dan-code1232/my-keeb/pcb/MY KEEB PCB FIXED.kicad_sch

## KiCad design pcb/MY KEEB PCB FIXED.kicad_sch (2026-08-29)

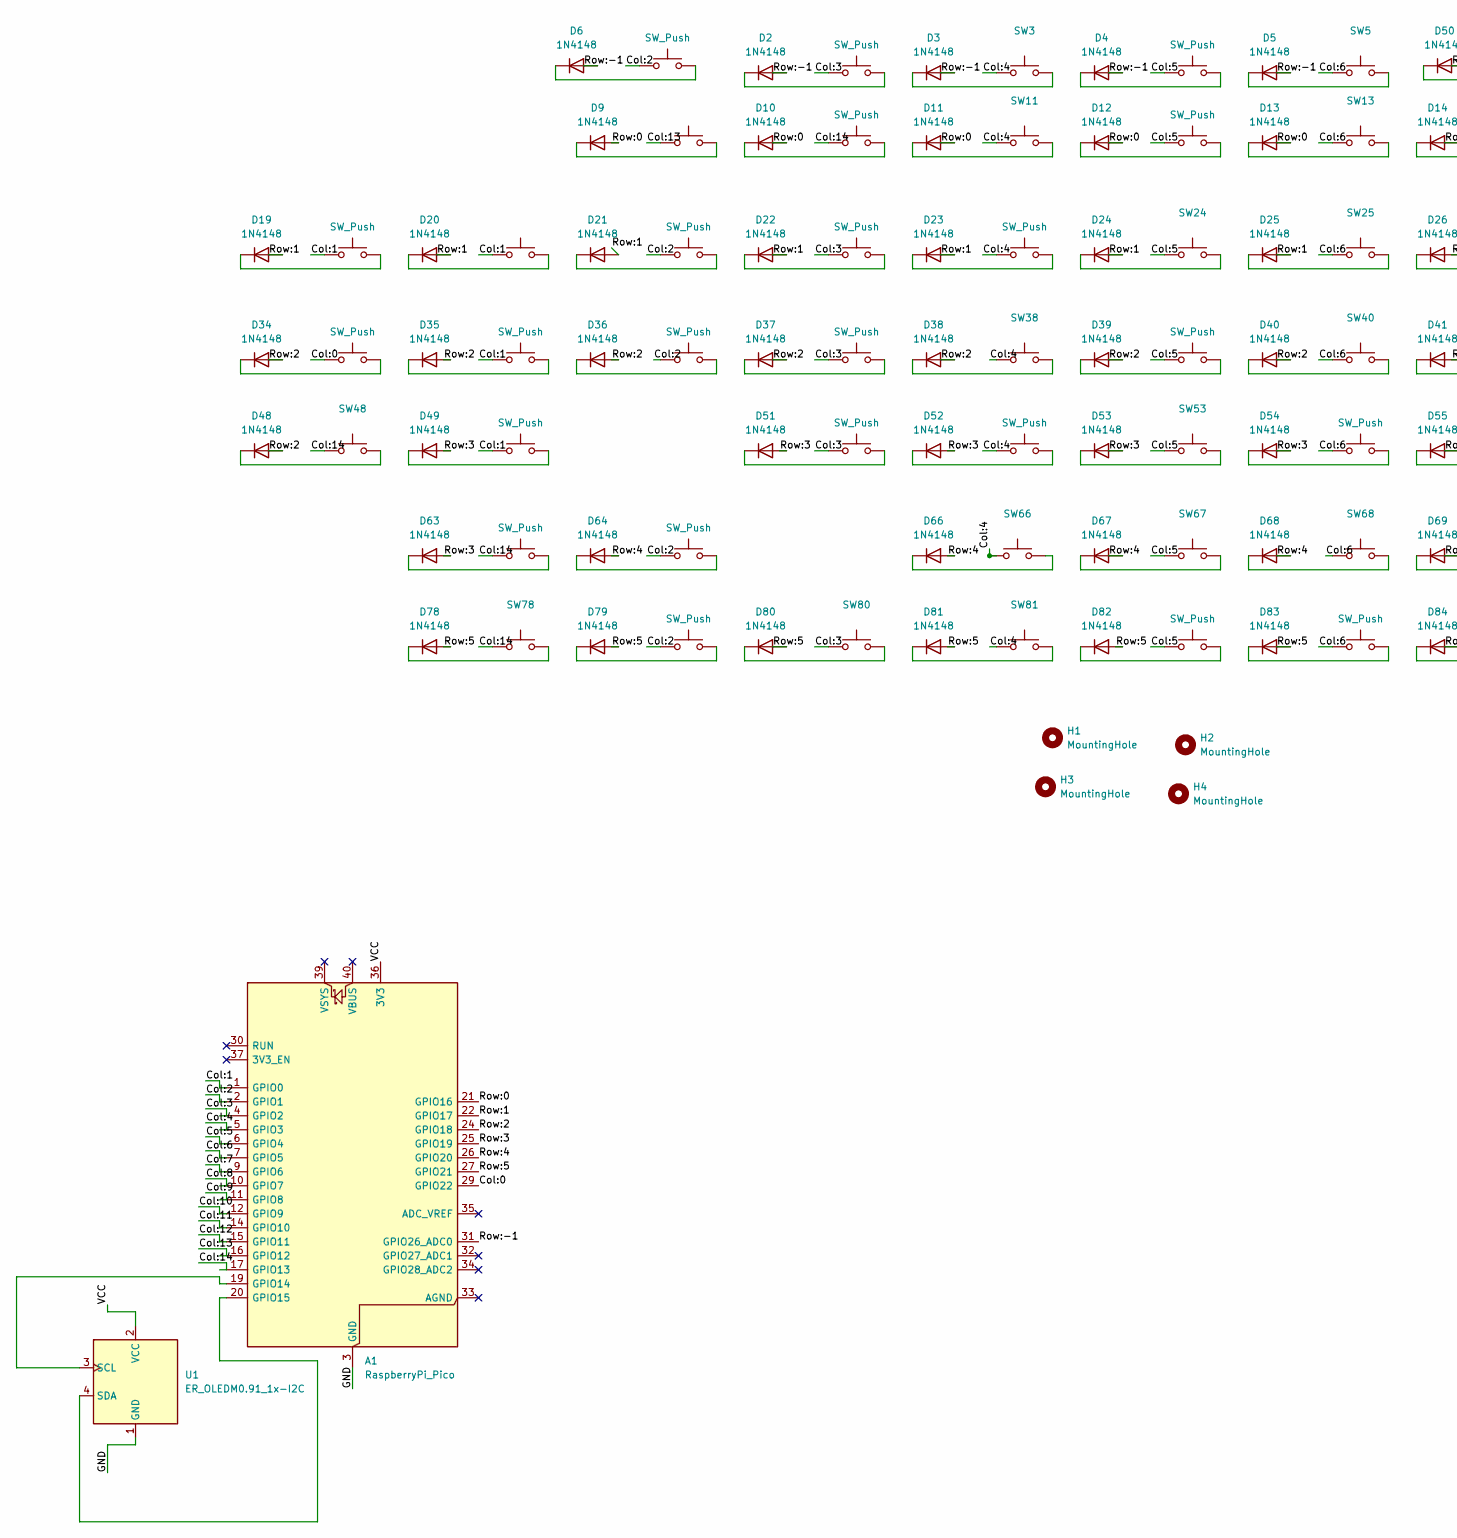
[picture p4: schematic MY KEEB PCB FIXED.kicad_sch, part in row 1, column 1]

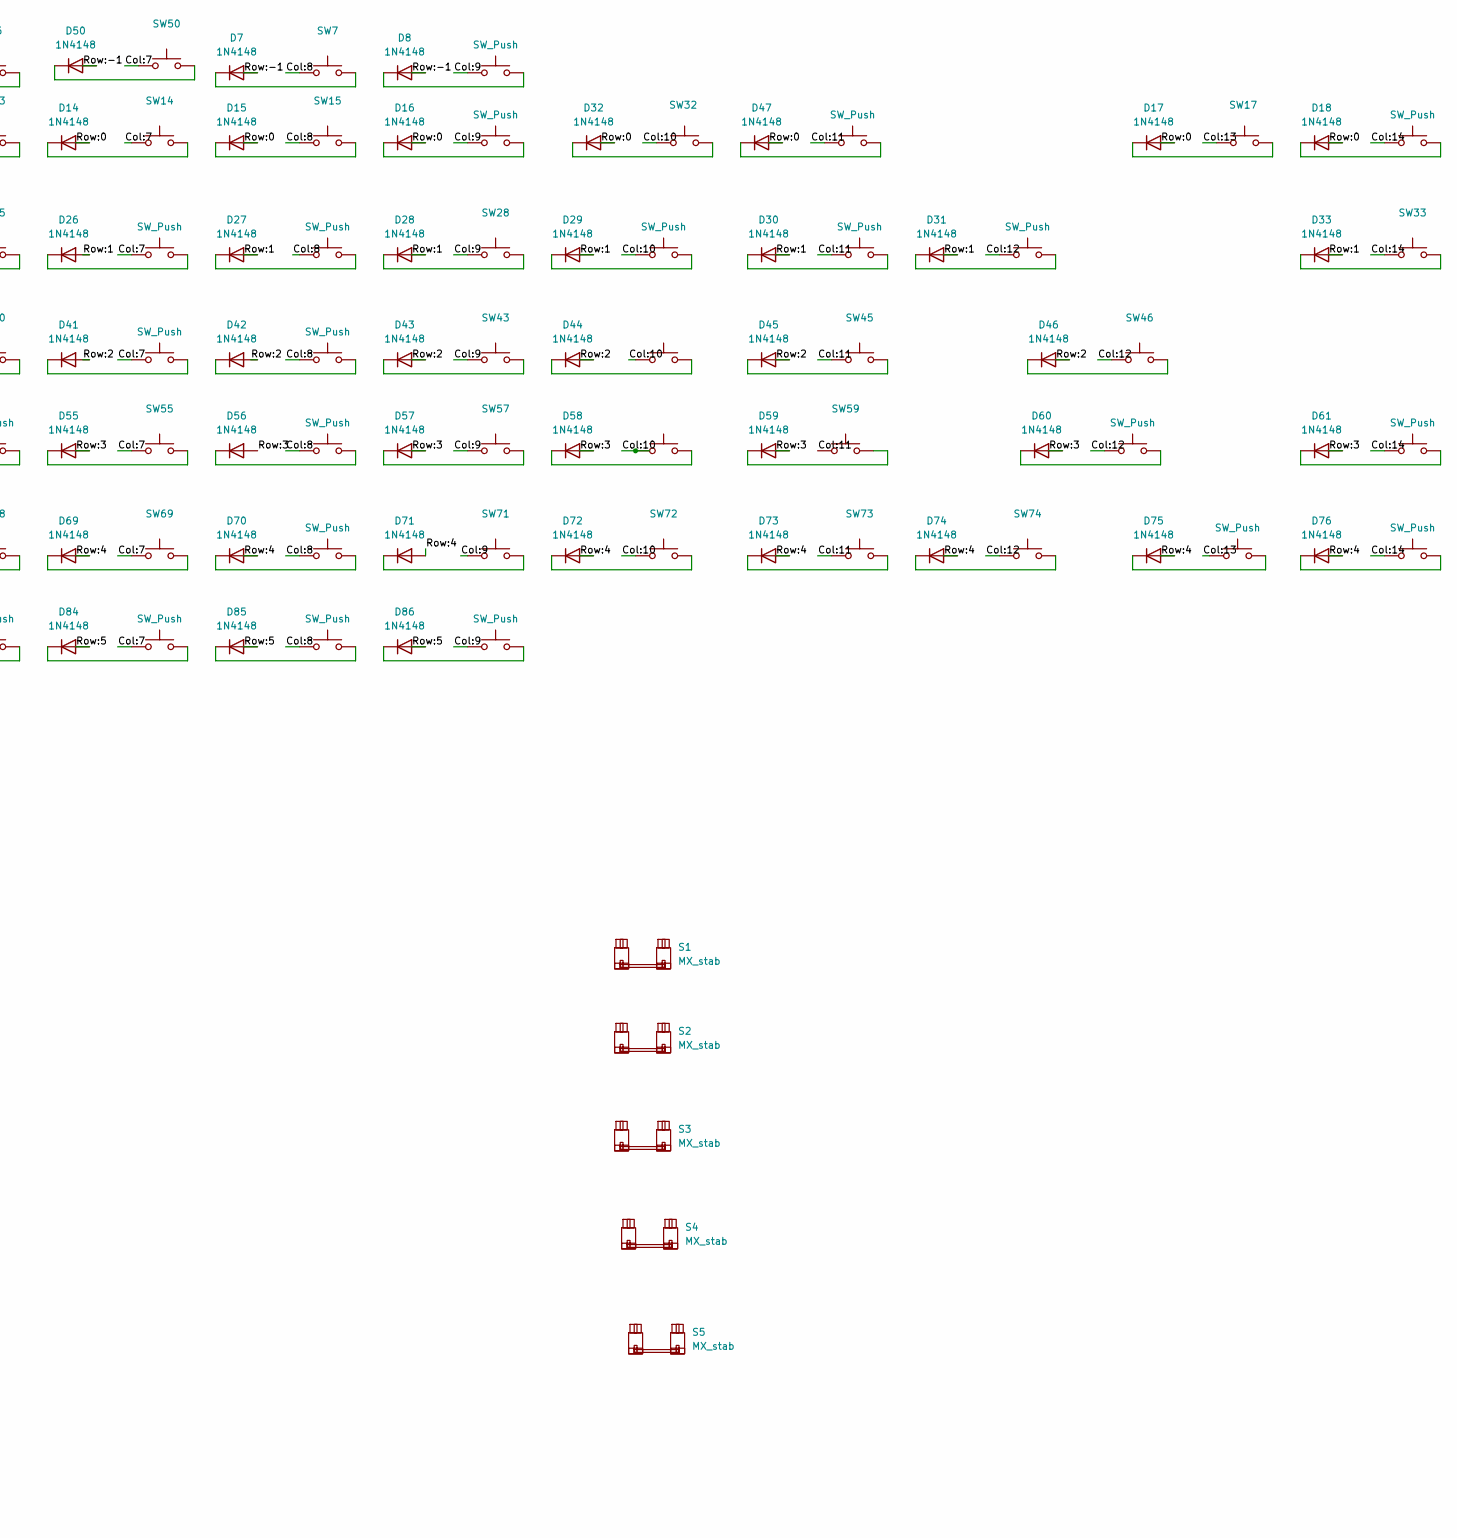
[picture p5: schematic MY KEEB PCB FIXED.kicad_sch, part in row 1, column 2]

Parts:
A1: RaspberryPi_Pico; RaspberryPi_Pico_Common_THT
D2, D3, D4, D5, D6, D7, D8, D9, D10, D11, D12, D13, D14, D15, D16, D17, D18, D19, D20, D21, D22, D23, D24, D25, D26, D27, D28, D29, D30, D31, D32, D33, D34, D35, D36, D37, D38, D39, D40, D41, D42, D43, D44, D45, D46, D47, D48, D49, D50, D51, D52, D53, D54, D55, D56, D57, D58, D59, D60, D61, D63, D64, D66, D67, D68, D69, D70, D71, D72, D73, D74, D75, D76, D78, D79, D80, D81, D82, D83, D84, D85, D86: 1N4148; D_DO-35_SOD27_P7.62mm_Horizontal
H1, H2, H3, H4: MountingHole; MountingHole_3.2mm_M3
S1, S2: MX_stab; STAB_MX_2.25u
S3: MX_stab; STAB_MX_P_6.25u
S4: MX_stab; STAB_MX_2.75u
S5: MX_stab; STAB_MX_2u
SW2, SW3, SW4, SW5, SW6, SW7, SW8, SW9, SW10, SW11, SW12, SW13, SW14, SW15, SW16, SW17, SW18, SW19, SW20, SW21, SW22, SW23, SW24, SW25, SW26, SW27, SW28, SW29, SW30, SW31, SW32, SW33, SW34, SW35, SW36, SW37, SW38, SW39, SW40, SW41, SW42, SW43, SW44, SW45, SW46, SW47, SW48, SW49, SW50, SW51, SW52, SW53, SW54, SW55, SW56, SW57, SW58, SW59, SW60, SW61, SW63, SW64, SW66, SW67, SW68, SW69, SW70, SW71, SW72, SW73, SW74, SW75, SW76, SW78, SW79, SW80, SW81, SW82, SW83, SW84, SW85, SW86: SW_Push; SW_MX_1u
U1: ER_OLEDM0.91_1x-I2C

Connections:
Col:0: A1.29 (GPIO22), SW34.1
Col:1: A1.1 (GPIO0), SW19.1, SW20.1, SW35.1, SW49.1
Col:2: A1.2 (GPIO1), SW6.1, SW21.1, SW36.1, SW64.1, SW79.1
Col:3: A1.4 (GPIO2), SW2.1, SW22.1, SW37.1, SW51.1, SW80.1
Col:4: A1.5 (GPIO3), SW3.1, SW11.1, SW23.1, SW38.1, SW52.1, SW66.1, SW81.1
Col:5: A1.6 (GPIO4), SW4.1, SW12.1, SW24.1, SW39.1, SW53.1, SW67.1, SW82.1
Col:6: A1.7 (GPIO5), SW5.1, SW13.1, SW25.1, SW40.1, SW54.1, SW68.1, SW83.1
Col:7: A1.9 (GPIO6), SW14.1, SW26.1, SW41.1, SW50.1, SW55.1, SW69.1, SW84.1
Col:8: A1.10 (GPIO7), SW7.1, SW15.1, SW27.1, SW42.1, SW56.1, SW70.1, SW85.1
Col:9: A1.11 (GPIO8), SW8.1, SW16.1, SW28.1, SW43.1, SW57.1, SW71.1, SW86.1
Col:10: A1.12 (GPIO9), SW29.1, SW32.1, SW44.1, SW58.1, SW72.1
Col:11: A1.14 (GPIO10), SW30.1, SW45.1, SW47.1, SW59.1, SW73.1
Col:12: A1.15 (GPIO11), SW31.1, SW46.1, SW60.1, SW74.1
Col:13: A1.16 (GPIO12), SW9.1, SW17.1, SW75.1
Col:14: A1.17 (GPIO13), SW10.1, SW18.1, SW33.1, SW48.1, SW61.1, SW63.1, SW76.1, SW78.1
GND: A1.3 (GND), A1.8 (GND), A1.13 (GND), A1.18 (GND), A1.23 (GND), A1.28 (GND), A1.38 (GND), U1.1 (GND)
unnamed: A1.19 (GPIO14), U1.3 (SCL)
unnamed: A1.20 (GPIO15), U1.4 (SDA)
unnamed: D2.1 (K), SW2.2
unnamed: D3.1 (K), SW3.2
unnamed: D4.1 (K), SW4.2
unnamed: D5.1 (K), SW5.2
unnamed: D6.1 (K), SW6.2
unnamed: D7.1 (K), SW7.2
unnamed: D8.1 (K), SW8.2
unnamed: D9.1 (K), SW9.2
unnamed: D10.1 (K), SW10.2
unnamed: D11.1 (K), SW11.2
unnamed: D12.1 (K), SW12.2
unnamed: D13.1 (K), SW13.2
unnamed: D14.1 (K), SW14.2
unnamed: D15.1 (K), SW15.2
unnamed: D16.1 (K), SW16.2
unnamed: D17.1 (K), SW17.2
unnamed: D18.1 (K), SW18.2
unnamed: D19.1 (K), SW19.2
unnamed: D20.1 (K), SW20.2
unnamed: D21.1 (K), SW21.2
unnamed: D22.1 (K), SW22.2
unnamed: D23.1 (K), SW23.2
unnamed: D24.1 (K), SW24.2
unnamed: D25.1 (K), SW25.2
unnamed: D26.1 (K), SW26.2
unnamed: D27.1 (K), SW27.2
unnamed: D28.1 (K), SW28.2
unnamed: D29.1 (K), SW29.2
unnamed: D30.1 (K), SW30.2
unnamed: D31.1 (K), SW31.2
unnamed: D32.1 (K), SW32.2
unnamed: D33.1 (K), SW33.2
unnamed: D34.1 (K), SW34.2
unnamed: D35.1 (K), SW35.2
unnamed: D36.1 (K), SW36.2
unnamed: D37.1 (K), SW37.2
unnamed: D38.1 (K), SW38.2
unnamed: D39.1 (K), SW39.2
unnamed: D40.1 (K), SW40.2
unnamed: D41.1 (K), SW41.2
unnamed: D42.1 (K), SW42.2
unnamed: D43.1 (K), SW43.2
unnamed: D44.1 (K), SW44.2
unnamed: D45.1 (K), SW45.2
unnamed: D46.1 (K), SW46.2
unnamed: D47.1 (K), SW47.2
unnamed: D48.1 (K), SW48.2
unnamed: D49.1 (K), SW49.2
unnamed: D50.1 (K), SW50.2
unnamed: D51.1 (K), SW51.2
unnamed: D52.1 (K), SW52.2
unnamed: D53.1 (K), SW53.2
unnamed: D54.1 (K), SW54.2
unnamed: D55.1 (K), SW55.2
unnamed: D56.1 (K), SW56.2
unnamed: D57.1 (K), SW57.2
unnamed: D58.1 (K), SW58.2
unnamed: D59.1 (K), SW59.2
unnamed: D60.1 (K), SW60.2
unnamed: D61.1 (K), SW61.2
unnamed: D63.1 (K), SW63.2
unnamed: D64.1 (K), SW64.2
unnamed: D66.1 (K), SW66.2
unnamed: D67.1 (K), SW67.2
unnamed: D68.1 (K), SW68.2
unnamed: D69.1 (K), SW69.2
unnamed: D70.1 (K), SW70.2
unnamed: D71.1 (K), SW71.2
unnamed: D72.1 (K), SW72.2
unnamed: D73.1 (K), SW73.2
unnamed: D74.1 (K), SW74.2
unnamed: D75.1 (K), SW75.2
unnamed: D76.1 (K), SW76.2
unnamed: D78.1 (K), SW78.2
unnamed: D79.1 (K), SW79.2
unnamed: D80.1 (K), SW80.2
unnamed: D81.1 (K), SW81.2
unnamed: D82.1 (K), SW82.2
unnamed: D83.1 (K), SW83.2
unnamed: D84.1 (K), SW84.2
unnamed: D85.1 (K), SW85.2
unnamed: D86.1 (K), SW86.2
Row:0: A1.21 (GPIO16), D9.2 (A), D10.2 (A), D11.2 (A), D12.2 (A), D13.2 (A), D14.2 (A), D15.2 (A), D16.2 (A), D17.2 (A), D18.2 (A), D32.2 (A), D47.2 (A)
Row:1: A1.22 (GPIO17), D19.2 (A), D20.2 (A), D21.2 (A), D22.2 (A), D23.2 (A), D24.2 (A), D25.2 (A), D26.2 (A), D27.2 (A), D28.2 (A), D29.2 (A), D30.2 (A), D31.2 (A), D33.2 (A)
Row:2: A1.24 (GPIO18), D34.2 (A), D35.2 (A), D36.2 (A), D37.2 (A), D38.2 (A), D39.2 (A), D40.2 (A), D41.2 (A), D42.2 (A), D43.2 (A), D44.2 (A), D45.2 (A), D46.2 (A), D48.2 (A)
Row:3: A1.25 (GPIO19), D49.2 (A), D51.2 (A), D52.2 (A), D53.2 (A), D54.2 (A), D55.2 (A), D56.2 (A), D57.2 (A), D58.2 (A), D59.2 (A), D60.2 (A), D61.2 (A), D63.2 (A)
Row:4: A1.26 (GPIO20), D64.2 (A), D66.2 (A), D67.2 (A), D68.2 (A), D69.2 (A), D70.2 (A), D71.2 (A), D72.2 (A), D73.2 (A), D74.2 (A), D75.2 (A), D76.2 (A)
Row:5: A1.27 (GPIO21), D78.2 (A), D79.2 (A), D80.2 (A), D81.2 (A), D82.2 (A), D83.2 (A), D84.2 (A), D85.2 (A), D86.2 (A)
Row:-1: A1.31 (GPIO26_ADC0), D2.2 (A), D3.2 (A), D4.2 (A), D5.2 (A), D6.2 (A), D7.2 (A), D8.2 (A), D50.2 (A)
VCC: A1.36 (3V3), U1.2 (VCC)
